Molegvas/MySERCOM/documents/resources/Charge_15A.png

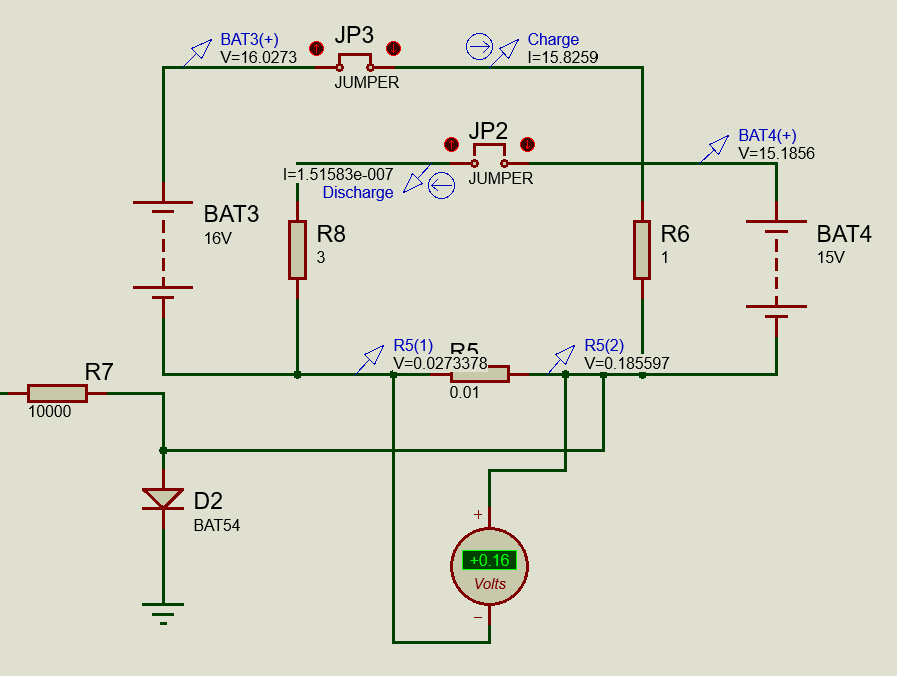
documents/resources/Charge_15A.png
