Molegvas/MySERCOM/documents/resources/D20v05bot.png

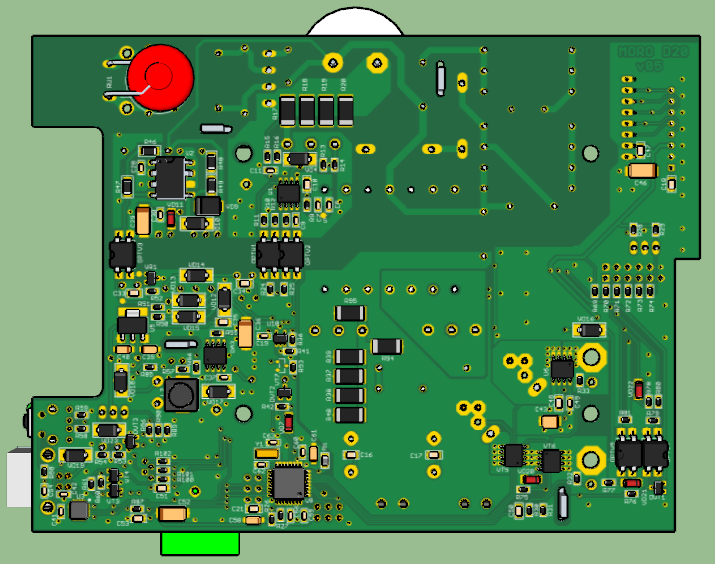
documents/resources/D20v05bot.png
