Molegvas/MySERCOM/documents/resources/Order.png

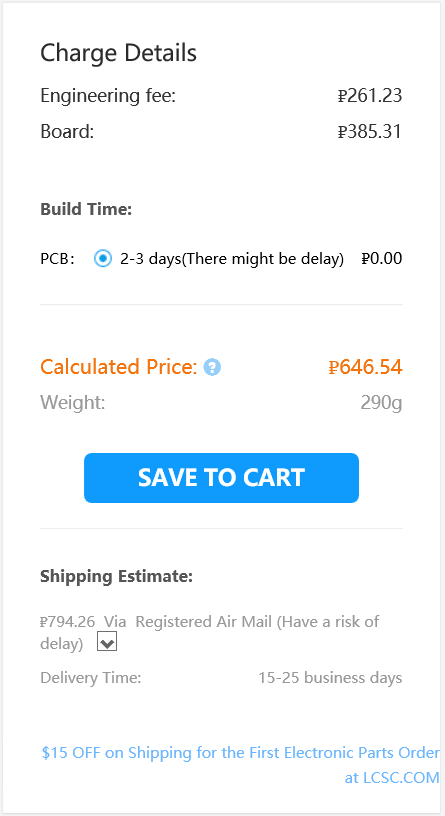
documents/resources/Order.png
