Molegvas/MySERCOM/src/commands/pid_commands.h

#ifndef _PID_COMMANDS_H_
#define _PID_COMMANDS_H_
/*


*/

#include "stdint.h"

void doPidTest();
//void doPidCoefficients();
//void doPidOutputConfig();
void doPidOutputRange();
void doPidConfigure();
void doPidClear();

#endif  //!_PID_COMMANDS_H_ 
